brettdottech/info-orbs/images/ClockWidget/nixie.holes/0.jpg

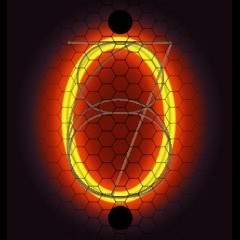
images/ClockWidget/nixie.holes/0.jpg
