brettdottech/info-orbs/images/ClockWidget/nixie.holes/1.jpg

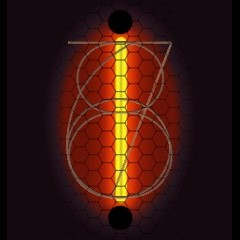
images/ClockWidget/nixie.holes/1.jpg
