brettdottech/info-orbs/images/ClockWidget/nixie.holes/2.jpg

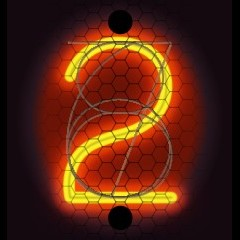
images/ClockWidget/nixie.holes/2.jpg
