brettdottech/info-orbs/images/ClockWidget/nixie.holes/3.jpg

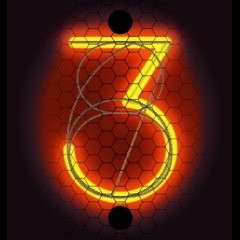
images/ClockWidget/nixie.holes/3.jpg
