brettdottech/info-orbs/images/ClockWidget/nixie.holes/4.jpg

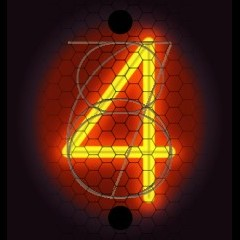
images/ClockWidget/nixie.holes/4.jpg
