brettdottech/info-orbs/images/ClockWidget/nixie.holes/5.jpg

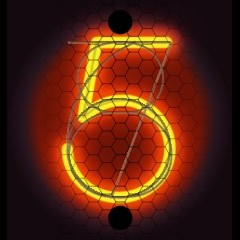
images/ClockWidget/nixie.holes/5.jpg
