brettdottech/info-orbs/images/ClockWidget/nixie.holes/6.jpg

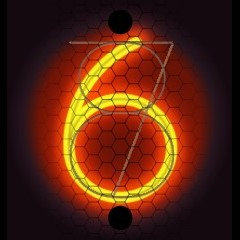
images/ClockWidget/nixie.holes/6.jpg
