brettdottech/info-orbs/images/ClockWidget/nixie.holes/7.jpg

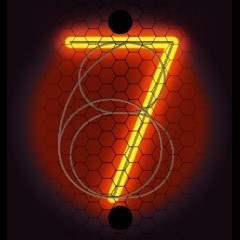
images/ClockWidget/nixie.holes/7.jpg
