brettdottech/info-orbs/images/ClockWidget/nixie.holes/8.jpg

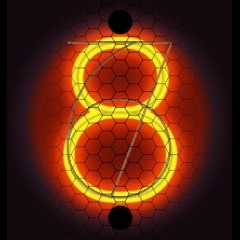
images/ClockWidget/nixie.holes/8.jpg
