brettdottech/info-orbs/images/ClockWidget/nixie.holes/9.jpg

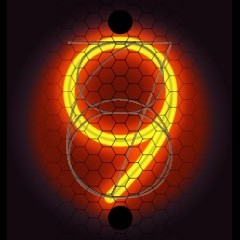
images/ClockWidget/nixie.holes/9.jpg
