brettdottech/info-orbs/images/ClockWidget/nixie.holes/colon_off.jpg

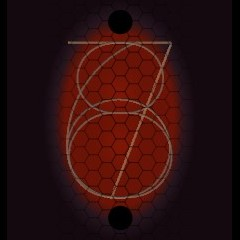
images/ClockWidget/nixie.holes/colon_off.jpg
