brettdottech/info-orbs/images/ClockWidget/nixie.no-holes/0.jpg

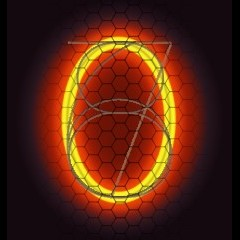
images/ClockWidget/nixie.no-holes/0.jpg
