brettdottech/info-orbs/images/ClockWidget/nixie.no-holes/2.jpg

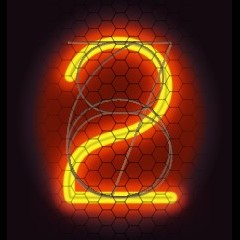
images/ClockWidget/nixie.no-holes/2.jpg
