brettdottech/info-orbs/images/ClockWidget/nixie.no-holes/7.jpg

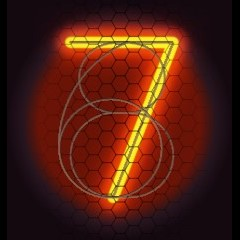
images/ClockWidget/nixie.no-holes/7.jpg
