brettdottech/info-orbs/images/ClockWidget/nixie.no-holes/8.jpg

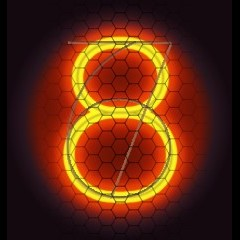
images/ClockWidget/nixie.no-holes/8.jpg
