brettdottech/info-orbs/images/WeatherWidget/dark/cloudsB.jpg

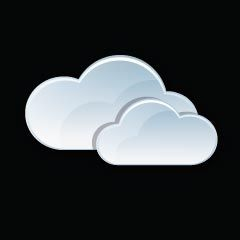
images/WeatherWidget/dark/cloudsB.jpg
