brettdottech/info-orbs/images/WeatherWidget/dark/moonB.jpg

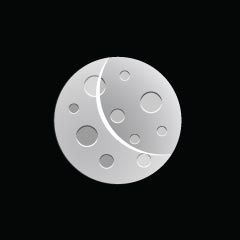
images/WeatherWidget/dark/moonB.jpg
