brettdottech/info-orbs/images/WeatherWidget/dark/moonCloudB.jpg

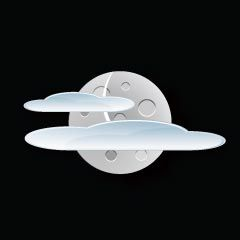
images/WeatherWidget/dark/moonCloudB.jpg
