brettdottech/info-orbs/images/WeatherWidget/dark/rainB.jpg

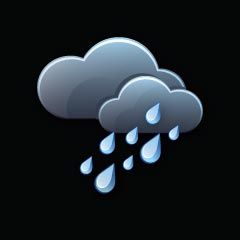
images/WeatherWidget/dark/rainB.jpg
