brettdottech/info-orbs/images/WeatherWidget/dark/snowB.jpg

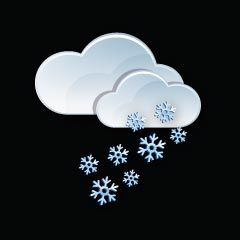
images/WeatherWidget/dark/snowB.jpg
