brettdottech/info-orbs/images/WeatherWidget/dark/sunB.jpg

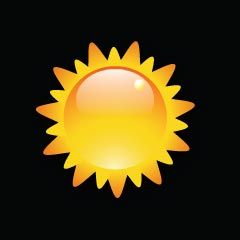
images/WeatherWidget/dark/sunB.jpg
