brettdottech/info-orbs/images/WeatherWidget/dark/sunCloudsB.jpg

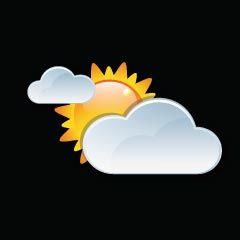
images/WeatherWidget/dark/sunCloudsB.jpg
