brettdottech/info-orbs/firmware/src/widgets/webdatawidget/WebDataElementArcModel.cpp

#include "WebDataElementArcModel.h"

int32_t WebDataElementArcModel::getX() {
    return m_x;
}

void WebDataElementArcModel::setX(int32_t x) {
    if (m_x != x) {
        m_x = x;
        m_changed = true;
    }
}

int32_t WebDataElementArcModel::getY() {
    return m_y;
}

void WebDataElementArcModel::setY(int32_t y) {
    if (m_y != y) {
        m_y = y;
        m_changed = true;
    }
}

int32_t WebDataElementArcModel::getRadius() {
    return m_radius;
}

void WebDataElementArcModel::setRadius(int32_t radius) {
    if (m_radius != radius) {
        m_radius = radius;
        m_changed = true;
    }
}

int32_t WebDataElementArcModel::getInnerRadius() {
    return m_innerRadius;
}

void WebDataElementArcModel::setInnerRadius(int32_t radius) {
    if (m_innerRadius != radius) {
        m_innerRadius = radius;
        m_changed = true;
    }
}

uint32_t WebDataElementArcModel::getAngleStart() {
    return m_angleStart;
}

void WebDataElementArcModel::setAngleStart(uint32_t angle) {
    if (m_angleStart != angle) {
        m_angleStart = angle;
        m_changed = true;
    }
}

uint32_t WebDataElementArcModel::getAngleEnd() {
    return m_angleEnd;
}

void WebDataElementArcModel::setAngleEnd(uint32_t angle) {
    if (m_angleEnd != angle) {
        m_angleEnd = angle;
        m_changed = true;
    }
}

int32_t WebDataElementArcModel::getBackgroundColor() {
    return m_background;
}

void WebDataElementArcModel::setBackgroundColor(int32_t background) {
    if (m_background != background) {
        m_background = background;
        m_changed = true;
    }
}

void WebDataElementArcModel::setBackgroundColor(String background) {
    setBackgroundColor(Utils::stringToColor(background));
}

void WebDataElementArcModel::setColor(int32_t color) {
    if (m_color != color) {
        m_color = color;
        m_changed = true;
    }
}

void WebDataElementArcModel::setColor(String color) {
    setColor(Utils::stringToColor(color));
}

int32_t WebDataElementArcModel::getColor() {
    return m_color;
}

void WebDataElementArcModel::parseData(const JsonObject &doc, int32_t defaultColor, int32_t defaultBackground) {
    if (doc["x"].is<int32_t>()) {
        setX(doc["x"].as<int32_t>());
    }
    if (doc["y"].is<int32_t>()) {
        setY(doc["y"].as<int32_t>());
    }
    if (doc["radius"].is<int32_t>()) {
        setRadius(doc["radius"].as<int32_t>());
    }
    if (doc["innerRadius"].is<int32_t>()) {
        setInnerRadius(doc["innerRadius"].as<int32_t>());
    }
    if (doc["angleStart"].is<int32_t>()) {
        setAngleStart(doc["angleStart"].as<int32_t>());
    }
    if (doc["angleEnd"].is<int32_t>()) {
        setAngleEnd(doc["angleEnd"].as<int32_t>());
    }
    if (const char *color = doc["color"]) {
        setColor(color);
    } else {
        setColor(defaultColor);
    }
    if (const char *background = doc["background"]) {
        setBackgroundColor(background);
    } else {
        setBackgroundColor(defaultBackground);
    }
}

void WebDataElementArcModel::draw(ScreenManager &manager) {
    manager.drawArc(getX(), getY(), getRadius(), getInnerRadius(), getAngleStart(), getAngleEnd(), getColor(), getBackgroundColor(), true);
}
