brettdottech/info-orbs/firmware/src/widgets/webdatawidget/WebDataElement.h

#ifndef WEB_DATA_ELEMENT_H
#define WEB_DATA_ELEMENT_H

#include "ScreenManager.h"
#include <ArduinoJson.h>

class WebDataElement {
public:
    virtual ~WebDataElement() = default;

    bool isChanged();
    void setChangedStatus(bool changed);

    virtual void parseData(const JsonObject &doc, int32_t defaultColor, int32_t defaultBackground);

    virtual void draw(ScreenManager &manager);

protected:
    bool m_changed = false;
};
#endif
